shajen/drink-maker/src/status_controller.cpp

#include <Arduino.h>
#include <config.h>
#include <logger.h>
#include <status_controller.h>

StatusController::StatusController() : m_frames(0), m_lastPrintStatusTime(0), m_fps(0.0f) {}

StatusController::~StatusController() {}

void StatusController::loop(const std::chrono::milliseconds& now) {
  if (m_lastPrintStatusTime + STATUS_PRINT_INTERVAL <= now) {
    m_fps = 1000.0f * m_frames / (now - m_lastPrintStatusTime).count();
    log("status", "fps: %.2f, free: %lu B", m_fps, ESP.getFreeHeap());
    m_frames = 0;
    m_lastPrintStatusTime = now;
  }
  m_frames++;
}

float StatusController::getFps() const { return m_fps; }
