shajen/drink-maker/src/settings.h

#pragma once

#include <helpers.h>

#include <chrono>

class Settings {
 public:
  Settings();

  Mode m_mode;
  int m_distance;
  int m_capacity;
  std::chrono::milliseconds m_glassDetectionDelay;
  std::chrono::milliseconds m_glassDisappearDelay;
  std::string m_primaryColor;
  std::string m_secondaryColor;
  bool m_isDebug;
  void save();
  void reset();

 private:
  void load(const char* filename);
  void save(const char* filename);
};
