shajen/drink-maker/src/ui_controller.cpp

#include "ui_controller.h"

#include <config.h>
#include <converter.h>
#include <logger.h>

using namespace std::placeholders;

constexpr auto LABEL = "ui";

const auto EMPTY_CALLBACK = [](Control*, int) {};
constexpr auto VIEW_CONTROL_COLOR = ControlColor::Peterriver;
constexpr auto NORMAL_BUTTON_CONTROL_COLOR = ControlColor::Emerald;
constexpr auto DANGER_BUTTON_CONTROL_COLOR = ControlColor::Alizarin;

template <typename T>
uint16_t createSelect(const uint16_t parent, const char* name, T& value, std::function<void()> changeValueCallback, std::vector<std::function<void()>>& readSettingsCallbacks) {
  const auto control = ESPUI.addControl(ControlType::Select, name, toString<T>(value), VIEW_CONTROL_COLOR, parent, [&value, changeValueCallback](Control* control, int) {
    value = fromString<T>(control->value);
    changeValueCallback();
  });
  readSettingsCallbacks.push_back([&value, control]() { ESPUI.updateControlValue(control, toString<T>(value)); });
  return control;
}

template <typename T>
uint16_t createSlider(
    const uint16_t parent,
    const char* name,
    T& value,
    const int min,
    const int max,
    const int step,
    std::function<void()> changeValueCallback,
    std::vector<std::function<void()>>& readSettingsCallbacks) {
  const auto control = ESPUI.addControl(ControlType::Slider, name, toString<T>(value), VIEW_CONTROL_COLOR, parent, [&value, changeValueCallback](Control* control, int) {
    value = fromString<T>(control->value);
    changeValueCallback();
  });
  readSettingsCallbacks.push_back([&value, control]() { ESPUI.updateControlValue(control, toString<T>(value)); });
  ESPUI.addControl(ControlType::Min, "min", String(min), VIEW_CONTROL_COLOR, control, EMPTY_CALLBACK);
  ESPUI.addControl(ControlType::Max, "max", String(max), VIEW_CONTROL_COLOR, control, EMPTY_CALLBACK);
  ESPUI.addControl(ControlType::Step, "step", String(step), VIEW_CONTROL_COLOR, control, EMPTY_CALLBACK);
  return control;
}

uint16_t createColor(const uint16_t parent, const char* name, std::string& value, std::function<void()> changeValueCallback, std::vector<std::function<void()>>& readSettingsCallbacks) {
  const auto control = ESPUI.addControl(ControlType::Text, name, toString<std::string>(value), VIEW_CONTROL_COLOR, parent, [&value, changeValueCallback](Control* control, int) {
    value = fromString<std::string>(control->value);
    changeValueCallback();
  });
  ESPUI.setInputType(control, "color");
  readSettingsCallbacks.push_back([&value, control]() { ESPUI.updateControlValue(control, toString<std::string>(value)); });
  return control;
}

uint16_t createSwitch(const uint16_t parent, const char* name, bool& value, std::function<void()> changeValueCallback, std::vector<std::function<void()>>& readSettingsCallbacks) {
  const auto control = ESPUI.addControl(ControlType::Switcher, name, toString<bool>(value), VIEW_CONTROL_COLOR, parent, [&value, changeValueCallback](Control* control, int) {
    value = fromString<bool>(control->value);
    changeValueCallback();
  });
  readSettingsCallbacks.push_back([&value, control]() { ESPUI.updateControlValue(control, toString<bool>(value)); });
  return control;
}

UiData::UiData() : m_pourCount(0), m_distanceErrorCount(0) {}

UiController::UiController(
    BatteryController& batteryController,
    const StatusController& statusController,
    const GlassDetector& glassDetector,
    const UiData& uiData,
    Settings& settings,
    std::function<void()> updateSettingsCallback,
    std::function<void()> manualPourCallback)
    : m_batteryController(batteryController),
      m_statusController(statusController),
      m_glassDetector(glassDetector),
      m_uiData(uiData),
      m_settings(settings),
      m_updateSettingsCallback(updateSettingsCallback),
      m_manualPourCallback(manualPourCallback),
      m_isDebugTab(false),
      m_lastPrintStatusTime(0) {
  const auto basicTab = ESPUI.addControl(ControlType::Tab, "basic settings", "basic settings", VIEW_CONTROL_COLOR, Control::noParent, [this](Control*, int) { m_isDebugTab = false; });
  const auto advancedTab = ESPUI.addControl(ControlType::Tab, "advanced settings", "advanced settings", VIEW_CONTROL_COLOR, Control::noParent, [this](Control*, int) { m_isDebugTab = false; });
  const auto debugTab = ESPUI.addControl(ControlType::Tab, "debug", "debug", VIEW_CONTROL_COLOR, Control::noParent, [this](Control*, int) { m_isDebugTab = true; });

  const auto modeSelect = createSelect(basicTab, "mode", m_settings.m_mode, std::bind(&UiController::saveSettings, this), m_readSettingsCallbacks);
  ESPUI.addControl(ControlType::Option, "auto", toString<Mode>(Mode::Auto), VIEW_CONTROL_COLOR, modeSelect);
  ESPUI.addControl(ControlType::Option, "manual", toString<Mode>(Mode::Manual), VIEW_CONTROL_COLOR, modeSelect);

  createSlider(basicTab, "capacity [ml]", m_settings.m_capacity, 10, 100, 5, std::bind(&UiController::saveSettings, this), m_readSettingsCallbacks);
  m_manualPourButton = ESPUI.addControl(ControlType::Button, "manual pour", "run", NORMAL_BUTTON_CONTROL_COLOR, basicTab, std::bind(&UiController::manualPour, this, _1, _2));
  ESPUI.addControl(ControlType::Button, "default settings", "run", DANGER_BUTTON_CONTROL_COLOR, basicTab, std::bind(&UiController::resetSettings, this, _1, _2));

  createSlider(advancedTab, "detection distance [cm]", m_settings.m_distance, 1, 100, 1, std::bind(&UiController::saveSettings, this), m_readSettingsCallbacks);
  createSlider(advancedTab, "glass detection delay [ms]", m_settings.m_glassDetectionDelay, 500, 10000, 100, std::bind(&UiController::saveSettings, this), m_readSettingsCallbacks);
  createSlider(advancedTab, "glass disappear delay [ms]", m_settings.m_glassDisappearDelay, 10, 1000, 10, std::bind(&UiController::saveSettings, this), m_readSettingsCallbacks);
  createColor(advancedTab, "primary color", m_settings.m_primaryColor, std::bind(&UiController::saveSettings, this), m_readSettingsCallbacks);
  createColor(advancedTab, "secondary color", m_settings.m_secondaryColor, std::bind(&UiController::saveSettings, this), m_readSettingsCallbacks);
  ESPUI.addControl(ControlType::Button, "default settings", "run", DANGER_BUTTON_CONTROL_COLOR, advancedTab, std::bind(&UiController::resetSettings, this, _1, _2));

  m_uptimeControl = ESPUI.addControl(ControlType::Label, "uptime", formatDuration(0ms).data(), VIEW_CONTROL_COLOR, debugTab);
  m_heapControl = ESPUI.addControl(ControlType::Label, "free heap [kB]", "0", VIEW_CONTROL_COLOR, debugTab);
  m_pourCountControl = ESPUI.addControl(ControlType::Label, "pour count", "0", VIEW_CONTROL_COLOR, debugTab);
  m_distanceControl = ESPUI.addControl(ControlType::Label, "distance [cm]", "0", VIEW_CONTROL_COLOR, debugTab);
  m_distanceErrorCountControl = ESPUI.addControl(ControlType::Label, "distance error count", "0", VIEW_CONTROL_COLOR, debugTab);
  m_fpsControl = ESPUI.addControl(ControlType::Label, "fps", "0", VIEW_CONTROL_COLOR, debugTab);
  m_batteryVoltageControl = ESPUI.addControl(ControlType::Label, "battery [V]", "0", VIEW_CONTROL_COLOR, debugTab);
  m_batteryPercentageControl = ESPUI.addControl(ControlType::Label, "battery [%]", "0", VIEW_CONTROL_COLOR, debugTab);
  ESPUI.addControl(ControlType::Label, "build time", BUILD_TIME, VIEW_CONTROL_COLOR, debugTab);
  ESPUI.addControl(ControlType::Label, "version", GIT_TAG, VIEW_CONTROL_COLOR, debugTab);
  ESPUI.addControl(ControlType::Label, "commit", GIT_COMMIT, VIEW_CONTROL_COLOR, debugTab);
  createSwitch(debugTab, "is debug", m_settings.m_isDebug, std::bind(&UiController::saveSettings, this), m_readSettingsCallbacks);
  ESPUI.addControl(ControlType::Button, "battery reset", "run", DANGER_BUTTON_CONTROL_COLOR, debugTab, std::bind(&UiController::batteryReset, this, _1, _2));
  ESPUI.addControl(ControlType::Button, "restart", "run", DANGER_BUTTON_CONTROL_COLOR, debugTab, std::bind(&UiController::reboot, this, _1, _2));

  ESPUI.beginLITTLEFS(HOSTNAME);
  updateManualPourButton();
}

UiController::~UiController() = default;

void UiController::loop(const std::chrono::milliseconds& now) {
  if (m_lastPrintStatusTime + UI_DEBUG_PRINT_INTERVAL <= now) {
    m_lastPrintStatusTime = now;
    if (m_isDebugTab) {
      ESPUI.updateControlValue(m_uptimeControl, formatDuration(now).data());
      ESPUI.updateNumber(m_heapControl, ESP.getFreeHeap() / 1024);
      ESPUI.updateNumber(m_pourCountControl, m_uiData.m_pourCount);
      ESPUI.updateNumber(m_distanceControl, m_glassDetector.getDistance());
      ESPUI.updateNumber(m_distanceErrorCountControl, m_uiData.m_distanceErrorCount);
      ESPUI.updateControlValue(m_fpsControl, String(m_statusController.getFps(), 2));
      ESPUI.updateControlValue(m_batteryVoltageControl, String(m_batteryController.getVoltage(), 2));
      ESPUI.updateNumber(m_batteryPercentageControl, m_batteryController.getPercentage(m_isDebugTab));
    }
  }
}

void UiController::updateManualPourButton() {
  log(LABEL, "update manual pour: %d", m_settings.m_mode == Mode::Manual);
  ESPUI.setEnabled(m_manualPourButton, m_settings.m_mode == Mode::Manual);
}

void UiController::saveSettings() {
  log(LABEL, "save settings");
  m_settings.save();
  m_updateSettingsCallback();
  updateManualPourButton();
}

void UiController::manualPour(Control* sender, int type) {
  if (type != B_UP) {
    return;
  }

  log(LABEL, "manual pour");
  m_manualPourCallback();
}

void UiController::resetSettings(Control* sender, int type) {
  if (type != B_UP) {
    return;
  }

  log(LABEL, "reset settings");
  m_settings.reset();
  m_updateSettingsCallback();
  for (const auto& callback : m_readSettingsCallbacks) {
    callback();
  }
  updateManualPourButton();
}

void UiController::batteryReset(Control* sender, int type) {
  if (type != B_UP) {
    return;
  }

  log(LABEL, "battery reset");
  m_batteryController.reset();
}

void UiController::reboot(Control* sender, int type) {
  if (type != B_UP) {
    return;
  }

  log(LABEL, "reboot");
  m_rebootTimer.once(1.0, []() { ESP.restart(); });
}
